dnkorte/DonKCar/arduino_code/nunchuk_feather_esp32s2/screen_tft.h

/*
 * Summary: openMV + esp32 based autonomous racer
 * 
 * Author(s):  Don Korte
 * Repository: https://github.com/dnkorte/DonKCar
 *
 * MIT License
 * Copyright (c) 2020 Don Korte
 * 
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
 * THE SOFTWARE IS PROVIDED "AS IS", WITHOUT WARRANTY OF ANY KIND, EXPRESS OR
 * IMPLIED, INCLUDING BUT NOT LIMITED TO THE WARRANTIES OF MERCHANTABILITY,
 * FITNESS FOR A PARTICULAR PURPOSE AND NONINFRINGEMENT. IN NO EVENT SHALL THE
 * AUTHORS OR COPYRIGHT HOLDERS BE LIABLE FOR ANY CLAIM, DAMAGES OR OTHER
 * LIABILITY, WHETHER IN AN ACTION OF CONTRACT, TORT OR OTHERWISE, ARISING FROM,
 * OUT OF OR IN CONNECTION WITH THE SOFTWARE OR THE USE OR OTHER DEALINGS IN THE
 * SOFTWARE. * 
 */

#include <Arduino.h>
#include "config.h"

#ifdef WANT_TFT
 
#ifndef SCREEN_H
#define SCREEN_H

//#include <Adafruit_SSD1306.h>
//#include <Adafruit_ST7735.h> // Hardware-specific library for ST7735
#include <Adafruit_ST7789.h> // Hardware-specific library for ST7789
#include <SPI.h>

#define SCREEN_WIDTH 240 // TFT display width, in pixels
#define SCREEN_HEIGHT 135 // TFT display height, in pixels

#define DEFAULT_SCALE 2
#define CHAR_WIDTH  (5*DEFAULT_SCALE)
#define CHAR_HEIGHT (7*DEFAULT_SCALE)
#define CELL_WIDTH  (CHAR_WIDTH+DEFAULT_SCALE)
#define CELL_HEIGHT (CHAR_HEIGHT+DEFAULT_SCALE)
#define CHARS_PER_LINE (SCREEN_WIDTH / CELL_WIDTH)
#define RIGHTMOST_COLUMN (CHARS_PER_LINE - 1)

#define NUM_ROWS 6

#define COL_LEFTEDGE 0
#define COL_DATA 5
#define WIDTH_HEADER 5
#define WIDTH_FULL CHARS_PER_LINE 
#define WIDTH_DATA (CHARS_PER_LINE - WIDTH_HEADER)

// screen locations for text
#define ROW_M_BATT1 0
#define ROW_M_NUNCHUK_INFO 1
#define ROW_M_STAT1 2
#define ROW_M_STAT2 3
#define ROW_M_STAT3 4
#define ROW_M_MENU_INFO 5

#define COL_M_BATT_LAB_E 0
#define COL_M_BATT_LAB_M 7
#define COL_M_BATT_LAB_C 14
//#define COL_M_NUN_X_LAB 0
//#define COL_M_NUN_Y_LAB 7
//#define COL_M_NUN_BTNS_LAB  15


//#define COL_LABEL_Y 0
//#define COL_VALUE_Y 2
//#define COL_LABEL_X 7
//#define COL_VALUE_X 9

#define COL_ROBOTNAME 0
#define COL_CMD_INFO 9

//#define COL_BTN_C 14
//#define COL_BTN_Z 15
//#define COL_BTN_0 13
//#define COL_BTN_1 13
//#define COL_BTN_2 13

#define COL_COMMSTAT 17
#define WIDTH_COMMSTAT 4

// RGB888 to 565 converter  https://trolsoft.ru/en/articles/rgb565-color-picker
// 565 color picker https://chrishewett.com/blog/true-rgb565-colour-picker/
// 565 color picker http://www.barth-dev.de/online/rgb565-color-picker/
// https://trolsoft.ru/en/articles/rgb565-color-picker  
// http://www.barth-dev.de/online/rgb565-color-picker/ 
// http://drakker.org/convert_rgb565.html

#define COLOR_FOREGROUND ST77XX_WHITE
#define COLOR_BACKGROUND ST77XX_BLACK
#define COLOR_HEADER ST77XX_BLUE
#define COLOR_RED ST77XX_RED
#define COLOR_MAGENTA ST77XX_MAGENTA
#define COLOR_ORANGE ST77XX_ORANGE
#define COLOR_YELLOW ST77XX_YELLOW
#define COLOR_GREEN ST77XX_GREEN
#define COLOR_BLUE ST77XX_BLUE
#define COLOR_CYAN ST77XX_CYAN
#define COLOR_WHITE ST77XX_WHITE
#define COLOR_BLACK ST77XX_BLACK
#define COLOR_PURPLE 0xB814

#define COLOR_GRAY 0x8430           // 0x888888
#define COLOR_LIGHT_GRAY 0xe75c     // 0xEEEEEE
#define COLOR_MED_GRAY 0xBDF7       // 0xC0C0C0
#define COLOR_DARK_GRAY 0x4228      // 0x484848
#define COLOR_ORANGE 0xFCE0         //  0xFFa000
#define COLOR_DARK_ORANGE  0xEC20   // 0xF18701
#define COLOR_LIGHT_BLUE  0x5C99    // 0x5C92D1
#define COLOR_PASTEL_GREEN  0x1EEF  // 0x19DF82
#define COLOR_SMOKY_GREEN 0x042D    // 0x03876D
#define COLOR_DARK_GREEN  0x04E0    // 0x00a000
#define COLOR_MELLOW_YELLOW 0xEF40  // 0xF4ED06
#define COLOR_LIGHT_YELLOW  0xFEE0  // 0xFFE000
#define COLOR_DARK_RED 0xD040       // 0xDE0A07
#define COLOR_PINK  0xFDF8          // 0xFFC0CB
#define COLOR_DEEP_PURPLE 0x8046    // 0x890C32
#define COLOR_VIOLET  0xD819        // 0xE300D2
#define COLOR_BROWN  0x91E4         // 0x9B3E25

void screen_init();
void screen_show();
void screen_clear();
void screen_clearLine(int rowindex);
void screen_clearField(int col, int rowindex, int nc);
void screen_dot_blink(int ulx, int uly, int color );
int screen_get_pixel_x(int col);
int screen_get_pixel_y(int rowindex);
int screen_get_last_col_index();
int ccToRGB(char colorcode);
void status_message_area_clear_check();

void screen_writeText_xrow(int x, int rowindex, int w, char myText[], int color );
void screen_writeText_colrow(int col, int rowindex, int nc, char myText[], int color );
void screen_writeString_xrow(int x, int rowindex, int w, String myString, int color );
void screen_writeString_colrow(int col, int rowindex, int nc, String myString, int color );

void screen_centerText(int rowindex, char myText[], int color);
void screen_centerString(int rowindex, String myString, int color);

#endif  /* SCREEN_H */
#endif  /* WANT_TFT */
